Tubatstuff/Pertec-Interface-Tape-Controller/firmware/inc/filesub.h

#ifndef _filesub_defined_
#define _filesub_defined_

//	File subroutines prototypes.

void MountSD( char *args[]);		// mount an SD card
void ChangeDir( char *args[]);
void MakeDir( char *args[]);
void ShowFiles( char *args[]);
void DeleteFile( char *args[]);
void SendFile( char *args[]);
void GetFile( char *args[]);
#endif
