Tubatstuff/Pertec-Interface-Tape-Controller/firmware/inc/license.h

/*         Copyright 2023, C. P. Guzis
		All rights reserved

 This software is provided by the copyright holder and contributors "AS IS"
 and any warranties related to this software are DISCLAIMED.
 The copyright owner or contributors be NOT LIABLE for any damages caused
 by use of this software.

 This software is licensed under the GNU General Public License, v3.0.
 For details, see https://www.gnu.org/licenses/gpl-3.0.en.html
 */
